BreakingKnees/Project-SAMUDRA/hardware/ltspice/AFE_draft1.asc

C1: cap; 120p
C2: cap; 100p
C3: cap; 180p
C4: cap; 68p
C5: cap; 10µ
C6: cap; 100n
C7: cap; 100n
R1: res; 13.8k
R2: res; 1.2k
R3: res; 1.2k
R4: res; 1.05k
R5: res; 1.05k
R6: res; 49.9
R7: res; 100k; pwr=0.25
R8: res; 50; pwr=0.25
U1A: UniversalOpAmp2
U1B: UniversalOpAmp2
U2A: UniversalOpAmp2
U2B: UniversalOpAmp2
V1: voltage; PWL file=Z:\home\ske\teamwork_projects\adaptive_sonar_transmitter\chirp.txt
V_NEG: voltage; 9
V_POS: voltage; 9
Named nets: 0, V_OUT, V+, V-
.tran 0 50u 40u 10n
